fahrian66/IoT-Modbus-Gateway/src/ambas.kicad_sch

## KiCad design src/ambas.kicad_sch (2025-07-21)

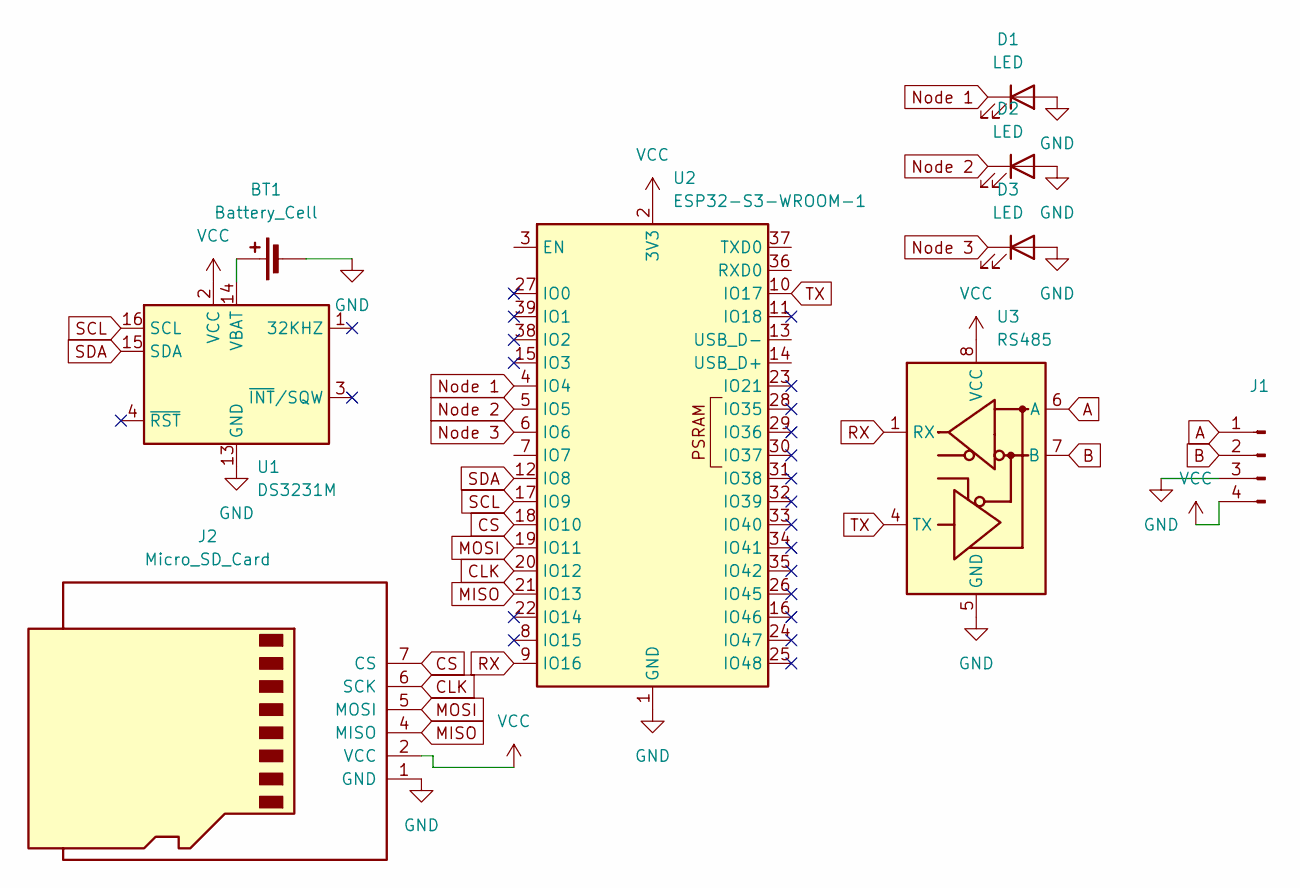
[picture p50: schematic ambas.kicad_sch]

Parts:
BT1: Battery_Cell
D1, D2, D3: LED
J1: Conn_01x04_Pin
J2: Micro_SD_Card
U1: DS3231M; SOIC-16W_7.5x10.3mm_P1.27mm
U2: ESP32-S3-WROOM-1
U3: RS485; SOIC-8_3.9x4.9mm_P1.27mm

Connections:
A: J1.1, U3.6 (A)
B: J1.2, U3.7 (B)
CLK: J2.6 (SCK), U2.20 (IO12)
CS: J2.7 (CS), U2.18 (IO10)
GND: BT1.2 (-), D1.2 (A), D2.2 (A), D3.2 (A), J1.3, J2.1 (GND), U1.5 (GND), U1.6 (GND), U1.7 (GND), U1.8 (GND), U1.9 (GND), U1.10 (GND), U1.11 (GND), U1.12 (GND), U1.13 (GND), U2.1 (GND), U2.40 (GND), U2.41 (GND), U3.5 (GND)
MISO: J2.4 (MISO), U2.21 (IO13)
MOSI: J2.5 (MOSI), U2.19 (IO11)
unnamed: BT1.1 (+), U1.14 (VBAT)
Node 1: D1.1 (K), U2.4 (IO4)
Node 2: D2.1 (K), U2.5 (IO5)
Node 3: D3.1 (K), U2.6 (IO6)
RX: U2.9 (IO16), U3.1 (RX)
SCL: U1.16 (SCL), U2.17 (IO9)
SDA: U1.15 (SDA), U2.12 (IO8)
TX: U2.10 (IO17), U3.4 (TX)
VCC: J1.4, J2.2 (VCC), U1.2 (VCC), U2.2 (3V3), U3.8 (VCC)
